KKosackH/SwitchSystemPublic/LibFiles/3DModels/R-78K5.0-2.0.stp

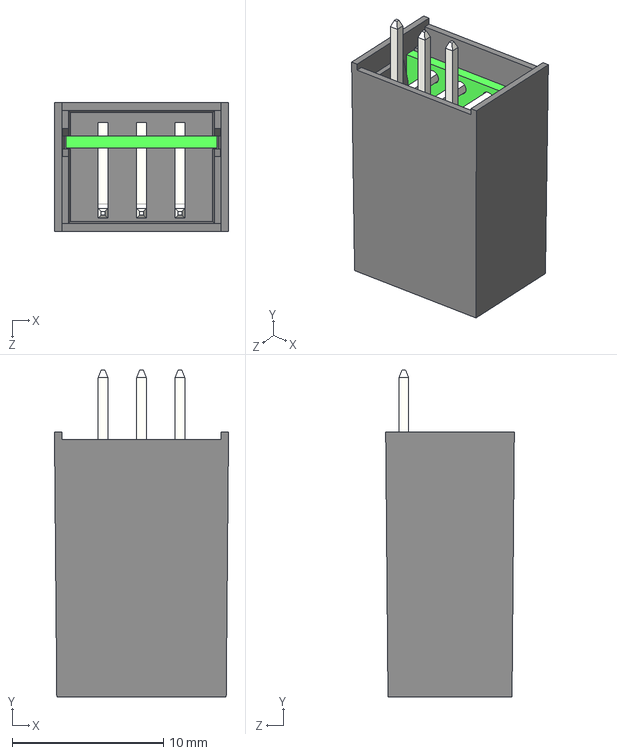
[picture p20: CAD file, 2025-10-05]
LibFiles/3DModels/R-78K5.0-2.0.stp
11.5 x 21.6 x 8.50 mm
