KKosackH/SwitchSystemPublic/LibFiles/3DModels/SMQW36R8JT.stp

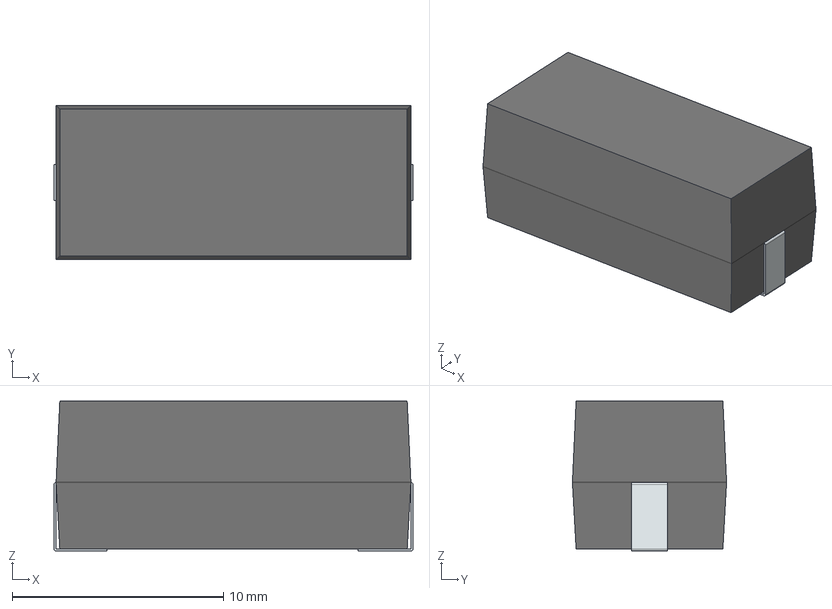
[picture p21: CAD file, 2025-10-05]
LibFiles/3DModels/SMQW36R8JT.stp
17.0 x 7.30 x 7.10 mm
FilletPin1
FilletPin2
