KKosackH/SwitchSystemPublic/LibFiles/3DModels/691709710302.stp

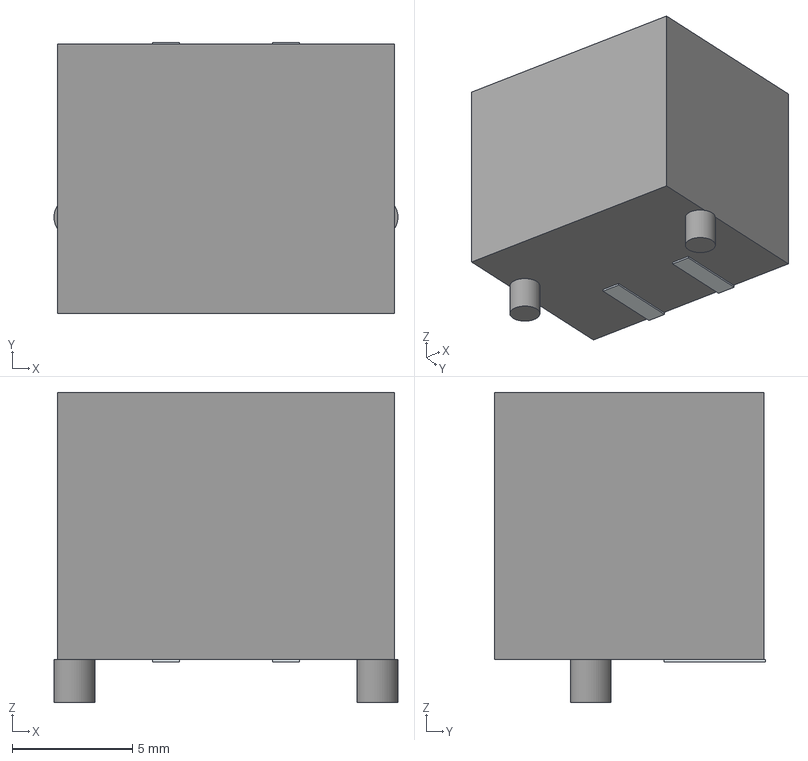
[picture p22: CAD file, 2025-10-05]
LibFiles/3DModels/691709710302.stp
14.3 x 11.3 x 12.9 mm
Pins
Lugs x 2
