KKosackH/SwitchSystemPublic/LibFiles/3DModels/1412410000.stp

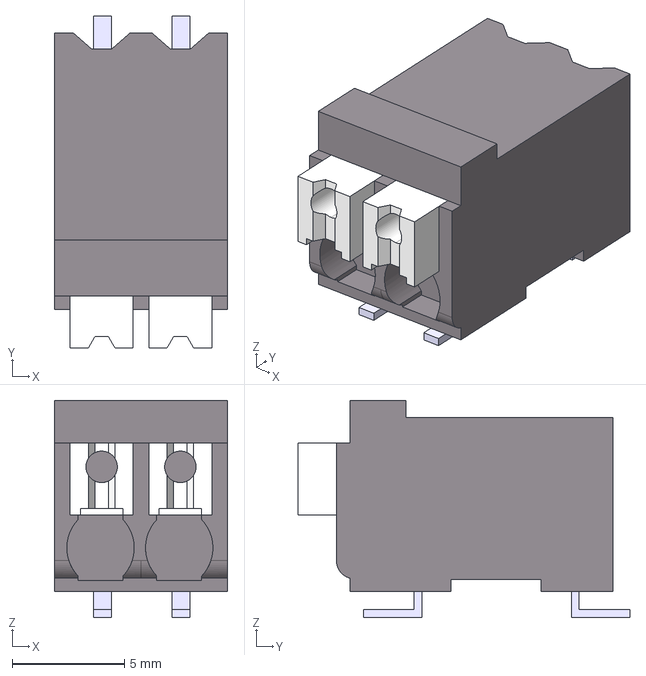
[picture p23: CAD file, 2025-10-05]
LibFiles/3DModels/1412410000.stp
7.70 x 14.8 x 9.65 mm
